IvanLi-CN/ups120/docs/pack_fet_selection.md

## BQ76200 PACK FET 选型报告（DFN5×6）

### 1. 背景与现状

- **电池平台**：项目基于 5S LiFePO₄（≈ 18 V 满电）电池包。SC8815 在异常复位时 VBAT 可能上冲至 ~36 V，需要保证 PACK 级 MOSFET 在该场景下仍安全工作（见 `DESIGN_MEMORANDUM.md`, `SC8815_External_Resistor_Configuration.md`）。
- **PACK 级拓扑**：根据最新网表 `docs/battery-pcb/netlist_battery.enet`，BQ76200（U3）通过 `CHG` / `DSG` 驱动两组背靠背 MOSFET：
  - **Q4 / Q8**：`NCEP6090AGU`（60 V, 90 A, DFN5×6-8L），源极接 `BAT`，漏极与对侧 FET 共结点 `$1N13010`。
  - **Q5 / Q9**：`NCEP40T13GU`（40 V, 130 A, DFN5×6-8L），源极接 `PACK_INNER_+`，漏极同样连接 `$1N13010`。
  - BQ76200 引脚 `CHG_EN/DSG_EN` 通过 nets `$1N12659`、`$1N12649` 分别控制 Q5/Q9 与 Q4/Q8 的栅极。
- **外部防护**：`D1 = SMBJ22A`（Vrwm=22 V, Vclamp≈35.5 V）位于 `PACK_INNER_+` 与 GND 之间，用于吸收负载侧感性尖峰。

> 结论：当前只有靠近电池侧的 FET（Q4/Q8）已换成 60 V 规格，靠近输出侧的 Q5/Q9 仍为 40 V 器件，在 VBAT 异常或 TVS 钳位上沿（≈35.5 V）时耐压裕量不足。

### 2. 驱动与选型约束

- **驱动能力**：BQ76200 内部充泵输出 9–14 V，等效上拉电阻约 1.1 kΩ、下拉 0.3 kΩ（TI SLUSC16B §6.5, §6.6）。对 40–90 nC 量级门电荷，开关时间在 5–10 µs，可满足保护动作需求。
- **耐压要求**：
  - 静态：5S LiFePO₄ 满电 ~18 V。
  - 异常：SC8815 寄存器复位引起 VBAT≈36 V。
  - 负载尖峰：由 D1 将 PACK 端限制在 35.5 V 左右。
  - 因此建议 FET V<sub>DS</sub> ≥ 60 V，优选 ≥ 65 V 以覆盖元件容差与 PCB 走线寄生。
- **封装兼容性**：现有 PCB 使用 DFN5×6-8L（Pad 尺寸 5.8×4.9 mm）。优先选择同封装以避免改版。

### 3. 备选器件比较（DFN5×6-8L）

| 型号 | V<sub>DS</sub> | Qg (typ) | Ciss | R<sub>DS(on)</sub> (典型) | I<sub>D</sub> (25 °C) | 单价 (¥)* | 资料 |
|---|---|---|---|---|---|---|---|
| **NCEP60T15G** | 60 V | 47 nC @10 V | 2.65 nF | 3.0 mΩ @10 V / 5.0 mΩ @4.5 V | 100 A | 2.65 | VBsemi `NCEP60T15G-VB.pdf` |
| **NCEP6090AGU** | 60 V | 67 nC @30 V | 4.00 nF | 2.8 mΩ @10 V / 3.5 mΩ @4.5 V | 90 A | 1.96 | NCE `ncep6090agu.pdf` |
| **NCEP035N85GU** | 85 V | 88 nC @10 V | 4.95 nF | 2.9 mΩ @10 V | 135 A | 2.94 | NCE `NCEP035N85GU.pdf` |

> *单价为同一渠道 2025-10-29 批量零购参考价（不含邮费），用于对比相对成本，实际采购以当期报价为准。

> 以上器件均与现有焊盘兼容，且门电荷在 BQ76200 的驱动能力范围之内。

### 4. 适配性评估

1. **耐压余量**  
   - 60 V 器件对 36 V 异常 + TVS 35.5 V 仍保留 >60 % 额定余量；40 V 器件裕量不足。  
   - 若外部系统可能施加更高母线或浪涌，可考虑 80–100 V 器件（如 NCEP035N85GU），但需评估额外门电荷与损耗。

2. **导通损耗与热**  
   - NCEP60T15G 和 TPHR6504PL 在 4.5–6 V 驱动下 R<sub>DS(on)</sub> 较低，有利于减小发热。  
   - NCEP6090AGU 已在 Q4/Q8 使用，可直接平移到 Q5/Q9，便于库存及 BOM 管理。  

3. **驱动裕度**  
   - BQ76200 以 1.1 kΩ 上拉驱动 50–90 nC 门电荷，开通时间约 5–8 µs（Qg ÷ (Vgate / R)）。与 datasheet 针对 10 nF 负载给出的 27–45 µs 设计值相比仍然留有余量。  
   - 更高 Qg（≥120 nC）器件会拖慢保护动作，不推荐。

### 5. 推荐方案

1. **统一更换 Q5 / Q9 为 60 V 器件**（保持 Q4 / Q8 为 60 V；形成四颗相同型号）  
   - **优选型号**：`NCEP60T15G`（低 Qg、低 R<sub>DS(on)</sub>），或直接延用 `NCEP6090AGU` 以简化供应。  
   - 若考虑 EMC/热设计极限，可评估 `TPHR6504PL` 作为备选。  
   - 高耐压备选 `NCEP035N85GU` 仅在需要额外裕度时使用，需要验证 6 V 驱动下的损耗。

2. **保留 SC8815 同步 FET（Q2/Q3/Q6/Q7）**：这几颗仍是 NCEP4090GU（40 V），仅承受电感两端电压，不直接面对 PACK 侧浪涌，本次无需调整。

### 6. 实施与验证计划

1. **BOM / 原理图更新**：将 Q5/Q9 型号改为推荐器件，并在 `docs/battery-pcb/netlist_battery.enet` 中保持一致。  
2. **样机验证**：焊接新 MOS 后，进行以下测试：  
   - 充电通路异常复位（VBAT≈36 V），确认 V<sub>DS</sub> 与温升。  
   - 放电通路断开感性负载，示波 PACK 电压，确认 TVS 钳位与 MOSFET 未过压。  
   - 长时间放电 / 充电，采集 FET 结温与效率。
3. **驱动波形检查**：测量 BQ76200 `CHG/DSG` 输出栅波形，必要时在栅极串入 1–2 Ω 阻尼以抑制振铃。  
4. **文件同步**：测试完成后，将结论写入 `DESIGN_MEMORANDUM.md`，并更新量产 BOM。

### 7. 结语

通过将 PACK 侧所有 DFN5×6 MOSFET 统一提升至 60 V 等级，可显著提高面对 VBAT 异常与外部尖峰的耐压裕度，同时保持与原 PCB 焊盘、电气驱动兼容。请在下一轮样机验证中重点关注动态浪涌与热表现，确认满足整机寿命与安全要求。***
