IvanLi-CN/ups120/docs/STM32L051C8_Index.md

# STM32L051C8 Datasheet (Markdown Parts)

Source: stm32l051c8.pdf

Parts:
- [Part 1: Pages 1–50](stm32l051c8/STM32L051C8_Part_001.md)
- [Part 2: Pages 51–100](stm32l051c8/STM32L051C8_Part_002.md)
- [Part 3: Pages 101–133](stm32l051c8/STM32L051C8_Part_003.md)
