IvanLi-CN/ups120/docs/rm0377/RM0377_STM32L0x1_Part_004.md

# RM0377 STM32L0x1 — Pages 151–200

**RM0377** **Power control (PWR)**

**6.3.7** **Sleep mode**

**I/O states in Sleep mode**

In Sleep mode, all I/O pins keep the same state as in Run mode.

**Entering Sleep mode**

The Sleep mode is entered according to _Section 6.3.5: Entering low-power mode_ .

Refer to _Table 35: Sleep-now_ and _Table 36: Sleep-on-exit_ for details on how to enter Sleep
mode.

**Exiting Sleep mode**

The Sleep mode is exited according to _Section 6.3.6: Exiting low-power mode_ .

Refer to _Table 35: Sleep-now_ and _Table 36: Sleep-on-exit_ for more details on how to exit
Sleep mode.

**Table 35. Sleep-now**

|Sleep-now mode|Description|
|---|---|
|Mode entry|WFI (Wait for Interrupt) or WFE (Wait for Event) while:<br>– SLEEPDEEP = 0 and<br>– No interrupt (for WFI) or event (for WFE) is pending<br>Refer to the Cortex®-M0+ System Control register (see PM0223 programming<br>manual).|
|Mode entry|On return from ISR while:<br>– SLEEPDEEP = 0 and<br>– SLEEPONEXIT = 1 and<br>– No interrupt is pending<br>Refer to the Cortex®-M0+ System Control register (see PM0223 programming<br>manual).|
|Mode exit|If WFI or return from ISR was used for entry:<br>Interrupt: refer to_Table 53: List of vectors_<br>If WFE was used for entry and SVONPEND = 0<br>Wakeup event: refer to_Section 12.3.2: Wakeup event management_<br>If WFE was used for entry and SVONPEND = 1<br>Interrupt event when disabled in NVIC (refer to_Table 53: List of vectors)_or<br>wakeup event (refer to_Section 12.3.2: Wakeup event management_)|
|Wakeup latency|None|

RM0377 Rev 10 151/905

166

--- end of page=150 ---

**Power control (PWR)** **RM0377**

**Table 36. Sleep-on-exit**

|Sleep-on-exit|Description|
|---|---|
|Mode entry|WFI (wait for interrupt) while:<br>– SLEEPDEEP = 0 and<br>– No interrupt (for WFI) or event (for WFE) is pending<br>Refer to the Cortex®-M0+ System Control register (see PM0223<br>programming manual).|
|Mode entry|On return from ISR while:<br>– SLEEPDEEP = 0 and<br>– SLEEPONEXIT = 1 and<br>– No interrupt is pending<br>Refer to the Cortex®-M0+ System Control register (see PM0223<br>programming manual).|
|Mode exit|Interrupt: refer to_Table 53: List of vectors_|
|Wakeup latency|None|

**6.3.8** **Low-power sleep mode (LP sleep)**

**I/O states in Low-power sleep mode**

In Low-power sleep mode, all I/O pins keep the same state as in Run mode.

**Entering Low-power sleep mode**

To enter Low-power sleep mode, proceed as follows:

1. The Flash memory can be switched off by using the control bits (SLEEP_PD in the
FLASH_ACR register. This reduces power consumption but increases the wake-up
time.

2. Each digital IP clock must be enabled or disabled by using the RCC_APBxENR and
RCC_AHBENR registers.

3. The frequency of the system clock must be decreased.

4. The regulator is forced in low-power mode by software (LPSDSR bits set).

5. Follow the steps described in _Section 6.3.5: Entering low-power mode_ .

Refer to _Table 37: Sleep-now (Low-power sleep)_ and _Table 38: Sleep-on-exit (Low-power_
_sleep)_ for details on how to enter Low-power sleep mode.

In Low-power sleep mode, the Flash memory can be switched off and the RAM memory
remains available.

In this mode, the system frequency should not exceed f_MSI range1.

Please refer to product datasheet for more details on voltage regulator and peripherals
operating conditions.

Low-power sleep mode can only be entered when V CORE is in range 2.

152/905 RM0377 Rev 10

--- end of page=151 ---

**RM0377** **Power control (PWR)**

_Note:_ _To be able to read the RTC calendar register when the APB1 clock frequency is less than_
_seven times the RTC clock frequency (7*RTCLCK), the software must read the calendar_
_time and date registers twice._

_If the second read of the RTC_TR gives the same result as the first read, this ensures that_
_the data is correct. Otherwise a third read access must be done._

**Exiting Low-power sleep mode**

The Low-power sleep mode is exited according to _Section 6.3.6: Exiting low-power mode_ .

When exiting Low-power sleep mode by issuing an interrupt or a wakeup event, the
regulator is configured in Main regulator mode, the Flash memory is switched on (if
necessary), and the system clock can be increased.

When the voltage regulator operates in low-power mode, an additional startup delay is
incurred when waking up from Low-power sleep mode.

Refer to _Table 37: Sleep-now (Low-power sleep)_ and _Table 38: Sleep-on-exit (Low-power_
_sleep)_ for more details on how to exit Sleep low-power mode.

**Table 37. Sleep-now (Low-power sleep)**

|Sleep-now mode|Description|
|---|---|
|Mode entry|Voltage regulator in low-power mode and the Flash memory switched off<br>WFI (Wait for Interrupt) or WFE (wait for event) while:<br>– SLEEPDEEP = 0 and<br>– No interrupt (for WFI) or event (for WFE) is pending<br>Refer to the Cortex®-M0+ System Control register (see PM0223 programming<br>manual).|
|Mode entry|On return from ISR while:<br>– SLEEPDEEP = 0 and<br>– SLEEPONEXIT = 1 and<br>– No interrupt is pending<br>Refer to the Cortex®-M0+ System Control register (see PM0223 programming<br>manual).|
|Mode exit|Voltage regulator in Main regulator mode and the Flash memory switched on<br>If WFI or Return from ISR was used for entry:<br>Interrupt: Refer to_Table 53: List of vectors_<br>If WFE was used for entry and SEVONPEND = 0<br>Wakeup event: Refer to_Section 12.3.2: Wakeup event management_<br>If WFE was used for entry and SVONPEND = 1<br>Interrupt event when disabled in NVIC (refer to_Table 53: List of vectors)_or<br>wakeup event (refer to_Section 12.3.2: Wakeup event management_)|
|Wakeup latency|Regulator wakeup time from low-power mode|

RM0377 Rev 10 153/905

166

--- end of page=152 ---

**Power control (PWR)** **RM0377**

**Table 38. Sleep-on-exit (Low-power sleep)**

|Sleep-on-exit|Description|
|---|---|
|Mode entry|WFI (wait for interrupt) while:<br>– SLEEPDEEP = 0 and<br>– No interrupt (for WFI) or event (for WFE) is pending<br>Refer to the Cortex®-M0+ System Control register (see PM0223<br>programming manual).|
|Mode entry|On return from ISR while:<br>– SLEEPDEEP = 0 and<br>– SLEEPONEXIT = 1 and<br>– No interrupt is pending<br>Refer to the Cortex®-M0+ System Control register (see PM0223<br>programming manual).|
|Mode exit|Interrupt: refer to_Table 53: List of vectors_.|
|Wakeup latency|regulator wakeup time from low-power mode|

**6.3.9** **Stop mode**

The Stop mode is based on the Cortex [®] -M0+ Deepsleep mode combined with peripheral
clock gating. The voltage regulator can be configured either in normal or low-power mode.
In Stop mode, all clocks in the V CORE domain are stopped, the PLL, the MSI, the HSI16
(except if HSI16KERON is set in Stop mode, see _Section 7.3.1: Clock control register_
_(RCC_CR)_ ) and the HSE RC oscillators are disabled. Internal SRAM and register contents
are preserved.

To get the lowest consumption in Stop mode, the internal Flash memory also enters lowpower mode. When the Flash memory is in power-down mode, an additional startup delay is
incurred when waking up from Stop mode.

To minimize the consumption In Stop mode, V REFINT, the BOR, PVD, and temperature
sensor can be switched off before entering Stop mode. This functionality is controlled by the
ULP bit in the PWR_CR register. If the ULP bit is set, the reference is switched off on Stop
mode entry and enabled again on wakeup. .

**I/O states in Low-power sleep mode**

In Stop mode, all I/O pins keep the same state as in Run mode.

**Entering Stop mode**

Refer to _Section 6.3.5: Entering low-power mode_ and to _Table 39_ for details on how to enter
the Stop mode.

If the application needs to disable the external clock before entering Stop mode, the HSEON
bit must be first disabled and the system clock switched to HSI16.

Otherwise, if the HSEON bit is kept enabled while external clock (external oscillator) can be
removed before entering Stop mode, the clock security system (CSS) feature must be
enabled to detect any external oscillator failure and avoid a malfunction behavior when
entering Stop mode.

154/905 RM0377 Rev 10

--- end of page=153 ---

**RM0377** **Power control (PWR)**

To further reduce power consumption in Stop mode, the internal voltage regulator can be put
in low-power mode. This is configured by the LPSDSR or LPDS bit in the PWR_CR register
(see _Section 6.4.1_ ). The internal voltage regulator can also be kept in Main mode but the
consumption will be much higher. As a result, it is always implicitly assumed that the
regulator is in low-power mode during Stop mode. The only advantage of keeping the
regulator in Main mode is that the wakeup time from Stop mode is shorter.

If Flash memory programming or an access to the APB domain is ongoing, the Stop mode
entry is delayed until the memory or APB access has completed.

In Stop mode, the following features can be selected by programming individual control bits:

      - Independent watchdog (IWDG): the IWDG is started by writing to its Key register or by
hardware option. Once started it cannot be stopped except by a Reset. Refer to
_Section 20.3: IWDG functional description_ in _Section 20: Independent watchdog_
_(IWDG)_ .

      - Real-time clock (RTC): this is configured by the RTCEN bit in the RCC_CSR register
(see _Section 7.3.20_ ).

      - Internal RC oscillator (LSI RC): this is configured by the LSION bit in the RCC_CSR
register.

      - External 32.768 kHz oscillator (LSE OSC): this is configured by the LSEON bit in the
RCC_CSR register.

The ADC can also consume power in Stop mode, unless they are disabled before entering
it. To disable them, the ADDIS bit in the ADC_CR register must be set to 1 must be written
to 0.

**Exiting Stop mode**

Refer to _Section 6.3.6: Exiting low-power mode_ and to _Table 39_ for details on how to exit
Stop mode.

When exiting Stop mode by issuing an interrupt or a wakeup event, the MSI or HSI16 RC
oscillator is selected as system clock depending the bit STOPWUCK in the RCC_CFGR
register.

When the voltage regulator operates in low-power mode, an additional startup delay is
incurred when waking up from Stop mode. By keeping the internal regulator ON during Stop
mode, the consumption is higher although the startup time is reduced.

RM0377 Rev 10 155/905

166

--- end of page=154 ---

**Power control (PWR)** **RM0377**

**Table 39. Stop mode**

|Stop mode|Description|
|---|---|
|Mode entry|WFI (Wait for Interrupt) or WFE (Wait for Event) while:<br>– No interrupt (for WFI) or event (for WFE) is pending.<br>– SLEEPDEEP bit is set in Cortex®-M0+ System Control register<br>– PDDS bit = 0 in Power Control register (PWR_CR)<br>– WUF bit = 0 in Power Control/Status register (PWR_CSR)<br>– MSI or HSI16 RC oscillator are selected as system clock for Stop mode<br>exit by configuring the STOPWUCK bit in the RCC_CFGR register.<br>_Note: To enter the Stop mode, all EXTI Line pending bits (in_<br>_Section 12.5.6: EXTI pending register (EXTI_PR)), all peripherals_<br>_interrupt pending bits, the RTC Alarm (Alarm A and Alarm B), RTC_<br>_wakeup, RTC tamper, and RTC time-stamp flags, must be reset._<br>_Otherwise, the Stop mode entry procedure is ignored and program_<br>_execution continues._|
|Mode entry|On return from ISR while:<br>– No interrupt is pending.<br>– SLEEPDEEP bit is set in Cortex®-M0+ System Control register<br>– SLEEPONEXIT = 1<br>– PDDS bit = 0 in Power Control register (PWR_CR)<br>– WUF bit = 0 in Power Control/Status register (PWR_CSR)<br>– MSI or HSI16 RC oscillator are selected as system clock for Stop mode<br>exit by configuring the STOPWUCK bit in the RCC_CFGR register.<br>_Note: To enter the Stop mode, all EXTI Line pending bits (in_<br>_Section 12.5.6: EXTI pending register (EXTI_PR)), all peripherals_<br>_interrupt pending bits, the RTC Alarm (Alarm A and Alarm B), RTC_<br>_wakeup, RTC tamper, and RTC time-stamp flags, must be reset._<br>_Otherwise, the Stop mode entry procedure is ignored and program_<br>_execution continues._|
|Mode exit|If WFI or return from ISR was used for entry:<br>Any EXTI Line configured in Interrupt mode (the corresponding EXTI<br>Interrupt vector must be enabled in the NVIC). Refer to_Table 53: List of_<br>_vectors._<br>If WFE was used for entry and SEVONPEND = 0<br>Any EXTI Line configured in event mode. Refer to_Section 12.3.2:_<br>_Wakeup event management on page 269_<br>If WFE was used for entry and SEVONPEND = 1<br>– Any EXTI Line configured in event mode (even if the corresponding EXTI<br>interrupt is disabled in the NVIC). The interrupt source can be an external<br>interrupt or a peripheral with wakeup capability (refer to_Table 53: List of_<br>_vectors)._<br>– A wakeup event (refer to_Section 12.3.2: Wakeup event management on_<br>_page 269_)|
|Wakeup latency|MSI or HSI16 RC wakeup time + regulator wakeup time from Low-power<br>mode + FLASH wakeup time|

156/905 RM0377 Rev 10

--- end of page=155 ---

**RM0377** **Power control (PWR)**

**6.3.10** **Standby mode**

The Standby mode allows to achieve the lowest power consumption. It is based on the
Cortex [®] -M0+ Deepsleep mode, with the voltage regulator disabled. The V CORE domain is
consequently powered off. The PLL, the MSI, the HSI16 oscillator and the HSE oscillator
are also switched off. SRAM and register contents are lost except for the RTC registers,
RTC backup registers and Standby circuitry (see _Figure 10_ ).

**I/O states in Standby mode**

In Standby mode, all I/O pins are high impedance except for:

      - Reset pad

      - Wakeup pins (WKUP1, WKUP2, WKUP3)

      - RTC functions (tamper, time-stamp, RTC Alarm out, RTC clock calibration out) on the
following I/Os:

–
Category 1: PA0, PA2

–
Category 2: PC13, PA0, PA2

–
Category 3: PC13, PA0

–
Category 5: PC13, PA0, PE6

**Entering Standby mode**

Refer to _Section 6.3.5: Entering low-power mode_ and to _Table 40_ for details on how to enter
Standby mode.

In Standby mode, the following features can be selected by programming individual control
bits:

      - Independent watchdog (IWDG): the IWDG is started by writing to its Key register or by
hardware option. Once started it cannot be stopped except by a reset. Refer to
_Section 20.3: IWDG functional description on page 528_ .

      - Real-time clock (RTC): this is configured by the RTCEN bit in the RCC_CSR register
(see _Section 7.3.20_ ).

      - Internal RC oscillator (LSI RC): this is configured by the LSION bit in the RCC_CSR
register.

      - External 32.768 kHz oscillator (LSE OSC): this is configured by the LSEON bit in the
RCC_CSR register.

**Exiting Standby mode**

The microcontroller exits Standby mode when an external Reset (NRST pin), an IWDG
Reset, a rising edge on WKUP pins (WUKP1, WKUP2 or WKUP3), an RTC alarm, a tamper
event, or a time-stamp event is detected.

After waking up from Standby mode, program execution restarts in the same way as after a
Reset (boot pins sampling, vector reset is fetched, etc.). The SBF status flag in the
PWR_CSR register (see _Section 6.4.2_ ) indicates that the microcontroller was in Standby
mode. All registers are reset to their default value after a system reset except for the register
bits in the RTC domain (see _Section 22.7: RTC registers_, SBF status flag in the _PWR power_
_control/status register (PWR_CSR)_, _Control/status register (RCC_CSR)_ and _Clock control_
_register (RCC_CR)_ ).

Refer to _Section 6.3.6: Exiting low-power mode_ and to _Table 40_ for more details on how to
exit Standby mode.

RM0377 Rev 10 157/905

166

--- end of page=156 ---

**Power control (PWR)** **RM0377**

**Table 40. Standby mode**

|Standby mode|Description|
|---|---|
|Mode entry|WFI (Wait for Interrupt) or WFE (Wait for Event) while:<br>– SLEEPDEEP = 1 in Cortex®-M0+ System Control register<br>– PDDS = 1 bit in Power Control register (PWR_CR)<br>– No interrupt (for WFI) or event (for WFE) is pending.<br>– WUF = 0 bit in Power Control/Status register (PWR_CSR)<br>– the RTC flag corresponding to the chosen wakeup source (RTC Alarm A,<br>RTC Alarm B, RTC wakeup, Tamper or Time-stamp flags) is cleared|
|Mode entry|On return from ISR while:<br>– SLEEPDEEP = 1 in Cortex®-M0+ System Control register<br>– SLEEPONEXIT = 1<br>– PDDS bit = 1 in Power Control register (PWR_CR)<br>– No interrupt is pending.<br>– WUF bit = 0 in Power Control/Status register (PWR_CSR)<br>– the RTC flag corresponding to the chosen wakeup source (RTC Alarm A,<br>RTC Alarm B, RTC wakeup, Tamper or Time-stamp flags) is cleared.|
|Mode exit|WKUP pin rising edge, RTC alarm (Alarm A and Alarm B), RTC wakeup,<br>tamper event, time-stamp event, external reset in NRST pin, IWDG reset.|
|Wakeup latency|Reset phase|

**Debug mode**

By default, the debug connection is lost if the application puts the MCU in Stop or Standby
mode while the debug features are used. This is due to the fact that the Cortex [®] -M0+ core is
no longer clocked.

However, by setting some configuration bits in the DBG_CR register, the software can be
debugged even when using the low-power modes extensively. For more details, refer to
_Section 27.9.1: Debug support for low-power modes_ .

**6.3.11** **Waking up the device from Stop and Standby modes using the RTC**
**and comparators**

The MCU can be woken up from low-power mode by an RTC Alarm event, an RTC Wakeup
event, a tamper event, a time-stamp event, or a comparator event, without depending on an
external interrupt (Auto-wakeup mode).

These RTC alternate functions can wake up the system from Stop and Standby low-power
modes while the comparator events can only wake up the system from Stop mode.

The system can also wake up from low-power modes without depending on an external
interrupt (Auto-wakeup mode) by using the RTC alarm or the RTC wakeup events.

158/905 RM0377 Rev 10

--- end of page=157 ---

**RM0377** **Power control (PWR)**

The RTC provides a programmable time base for waking up from Stop or Standby mode at
regular intervals. For this purpose, two of the three alternative RTC clock sources can be
selected by programming the RTCSEL[1:0] bits in the RCC_CSR register (see
_Section 7.3.20_ ):

      - Low-power 32.768 kHz external crystal oscillator (LSE OSC).
This clock source provides a precise time base with very low-power consumption (less
than 1 µA added consumption in typical conditions)

      - Low-power internal RC oscillator (LSI RC)

This clock source has the advantage of saving the cost of the 32.768 kHz crystal. This
internal RC Oscillator is designed to use minimum power consumption.

**RTC auto-wakeup (AWU) from the Stop mode**

      - To wake up from the Stop mode with an RTC alarm event, it is necessary to:

a) Configure the EXTI Line 17 to be sensitive to rising edges (Interrupt or Event
modes)

b) Enable the RTC Alarm interrupt in the RTC_CR register

c) Configure the RTC to generate the RTC alarm

      - To wake up from the Stop mode with an RTC Tamper or time stamp event, it is
necessary to:

a) Configure the EXTI Line 19 to be sensitive to rising edges (Interrupt or Event
modes)

b) Enable the RTC TimeStamp Interrupt in the RTC_CR register or the RTC Tamper
Interrupt in the RTC_TCR register

c) Configure the RTC to detect the tamper or time stamp event

      - To wake up from the Stop mode with an RTC Wakeup event, it is necessary to:

a) Configure the EXTI Line 20 to be sensitive to rising edges (Interrupt or Event
modes)

b) Enable the RTC Wakeup Interrupt in the RTC_CR register

c) Configure the RTC to generate the RTC Wakeup event

**RTC auto-wakeup (AWU) from the Standby mode**

      - To wake up from the Standby mode with an RTC alarm event, it is necessary to:

a) Enable the RTC Alarm interrupt in the RTC_CR register

b) Configure the RTC to generate the RTC alarm

      - To wake up from the Stop mode with an RTC Tamper or time stamp event, it is
necessary to:

a) Enable the RTC TimeStamp Interrupt in the RTC_CR register or the RTC Tamper
Interrupt in the RTC_TCR register

b) Configure the RTC to detect the tamper or time stamp event

      - To wake up from the Stop mode with an RTC Wakeup event, it is necessary to:

a) Enable the RTC Wakeup Interrupt in the RTC_CR register

b) Configure the RTC to generate the RTC Wakeup event

RM0377 Rev 10 159/905

166

--- end of page=158 ---

**Power control (PWR)** **RM0377**

**Comparator auto-wakeup (AWU) from the Stop mode**

      - To wake up from the Stop mode with a comparator 1 or comparator 2 wakeup event, it
is necessary to:

a) Configure the EXTI Line 21 for comparator 1 or EXTI Line 22 for comparator 2
(Interrupt or Event mode) to be sensitive to the selected edges (falling, rising or
falling and rising)

b) Configure the comparator to generate the event.

160/905 RM0377 Rev 10

--- end of page=159 ---

**RM0377** **Power control (PWR)**

###### **6.4 Power control registers**

The peripheral registers have to be accessed by half-words (16-bit) or words (32-bit).

**6.4.1** **PWR power control register (PWR_CR)**

Address offset: 0x00

Reset value: 0x0000 1000 (reset by wakeup from Standby mode)

|31|30|29|28|27|26|25|24|23|22|21|20|19|18|17|16|
|---|---|---|---|---|---|---|---|---|---|---|---|---|---|---|---|
|Res.|Res.|Res.|Res.|Res.|Res.|Res.|Res.|Res.|Res.|Res.|Res.|Res.|Res.|Res.|LPDS|
||||||||||||||||rw|

|15|14|13|12 11|Col5|10|9|8|7 6 5|Col10|Col11|4|3|2|1|0|
|---|---|---|---|---|---|---|---|---|---|---|---|---|---|---|---|
|Res.|LPRUN|DS_EE<br>_KOFF|VOS[1:0]|VOS[1:0]|FWU|ULP|DBP|PLS[2:0]|PLS[2:0]|PLS[2:0]|PVDE|CSBF|CWUF|PDDS|LPSDSR|
||rw|rw|rw|rw|rw|rw|rw|rw|rw|rw|rw|rc_w1|rc_w1|rw|rw|

Bits 31:17 Reserved, always read as 0.

Bit 16 **LPDS** : Regulator in Low-power deepsleep mode

This bit allows switching the regulator to low-power mode when the CPU enters Stop
mode. Its behavior depends on LPSDSR bit.

– if LPSDSR = 1: bit has no effect.

– if LPSDSR = 0:

0: Voltage regulator in Main mode during Deepsleep mode (Stop mode)
1: Voltage regulator switches to low-power mode when the CPU enters Deepsleep mode
(Stop mode).
The regulator goes back to Main mode when the CPU exits from Deepsleep mode.

_Note: The LPDS bit is available on category 1 devices only._

Bit 15 Reserved, always read as 0.

Bit 14 **LPRUN:** Low-power run mode

When LPRUN bit is set together with the LPSDSR bit, the regulator is switched from Main
mode to low-power mode. Otherwise, it remains in Main mode. The regulator goes back to
operate in Main mode when LPRUN is reset.
If this bit is set (with LPSDSR bit set) and the CPU enters sleep or Deepsleep mode (LP
sleep or Stop mode), then, when the CPU wakes up from these modes, it enters Run
mode but with LPRUN bit set. To enter again Low-power run mode, it is necessary to
perform a reset and set LPRUN bit again.
It is forbidden to reset LPSDSR when the MCU is in Low-power run mode. LPSDSR is
used as a prepositioning for the entry into low-power mode, indicating to the system which
configuration of the regulator will be selected when entering low-power mode. The
LPSDSR bit must be set before the LPRUN bit is set. LPSDSR can be reset only when
LPRUN bit=0.

0: Voltage regulator in Main mode in Low-power run mode
1: Voltage regulator in low-power mode in Low-power run mode

Bit 13 **DS_EE_KOFF** : Deepsleep mode with non-volatile memory kept off

When entering low-power mode (Stop or Standby only), if DS_EE_KOFF and RUN_PD
bits are both set in FLASH_ACR register (refer to _Section 3.7.1: Access control register_
_(FLASH_ACR)_, the non-volatile memory (Flash program memory and data EEPROM) will
not be woken up when exiting from Deepsleep mode.
0: NVM woken up when exiting from Deepsleep mode even if the bit RUN_PD is set
1: NVM not woken up when exiting from low-power mode (if the bit RUN_PD is set)

RM0377 Rev 10 161/905

166

--- end of page=160 ---

**Power control (PWR)** **RM0377**

Bits 12:11 **VOS[1:0]:** Voltage scaling range selection

These bits are used to select the internal regulator voltage range.
Before resetting the power interface by resetting the PWRRST bit in the RCC_APB1RSTR
register, these bits have to be set to ‘10’ and the frequency of the system has to be
configured accordingly.

00: forbidden (bits are unchanged and keep the previous value, no voltage change
occurs)
01: 1.8 V (range 1)
10: 1.5 V (range 2)
11: 1.2 V (range 3)

Bit 10 **FWU** : Fast wakeup

This bit works in conjunction with ULP bit.

If ULP = 0, FWU is ignored

If ULP = 1 and FWU = 1: V REFINT startup time is ignored when exiting from low-power mode.
The VREFINTRDYF flag in the PWR_CSR register indicates when the V REFINT is ready
again.

If ULP=1 and FWU = 0: Exiting from low-power mode occurs only when the V REFINT is ready
(after its startup time). This bit is not reset by resetting the PWRRST bit in the
RCC_APB1RSTR register.

0: Low-power modes exit occurs only when V REFINT is ready
1: V REFINT start up time is ignored when exiting low-power modes

Bit 9 **ULP** : Ultra-low-power mode

When set, the V REFINT is switched off in low-power mode. The BOR, PVD, and temperature
sensor also rely on the voltage reference. This bit is not reset by resetting the PWRRST bit
in the RCC_APB1RSTR register.

0: V REFINT is on in low-power mode
1: V REFINT is off in low-power mode

Bit 8 **DBP** : Disable backup write protection

In reset state, the RTC, RTC backup registers and RCC CSR register are protected against
parasitic write access. This bit must be set to enable write access to these registers.

0: Access to RTC, RTC Backup and RCC CSR registers disabled
1: Access to RTC, RTC Backup and RCC CSR registers enabled

_Note: If the HSE divided by 2, 4, 8 or 16 is used as the RTC clock, this bit must remain set_
_to 1._

Bits 7:5 **PLS[2:0]:** PVD level selection

These bits are written by software to select the voltage threshold detected by the
programmable voltage detector:

000: 1.9 V

001: 2.1 V

010: 2.3 V

011: 2.5 V

100: 2.7 V

101: 2.9 V

110: 3.1 V

111: External input analog voltage (Compare internally to V REFINT )
PVD_IN input (PB7) has to be configured as analog input when PLS[2:0] = 111.

_Note: Refer to the electrical characteristics of the datasheet for more details._

162/905 RM0377 Rev 10

--- end of page=161 ---

**RM0377** **Power control (PWR)**

Bit 4 **PVDE:** Programmable voltage detector enable

This bit is set and cleared by software.

0: PVD disabled

1: PVD enabled

Bit 3 **CSBF** : Clear standby flag

This bit is always read as 0.

0: No effect

1: Clear the SBF Standby flag (write).

Bit 2 **CWUF:** Clear wakeup flag

This bit is always read as 0.

0: No effect

1: Clear the WUF Wakeup flag after 2 system clock cycles

Bit 1 **PDDS** : Power-down deepsleep

This bit is set and cleared by software.

0: Enter Stop mode when the CPU enters Deepsleep.
1: Enter Standby mode when the CPU enters Deepsleep.

Bit 0 **LPSDSR:** Low-power deepsleep/Sleep/Low-power run

– DeepSleep/Sleep modes

When this bit is set, the regulator switches in low-power mode when the CPU enters sleep
or Deepsleep mode. The regulator goes back to Main mode when the CPU exits from
these modes.

– Low-power run mode

When this bit is set, the regulator switches in low-power mode when the bit LPRUN is set.
The regulator goes back to Main mode when the bit LPRUN is reset.

This bit is set and cleared by software.

0: Voltage regulator on during Deepsleep/Sleep/Low-power run mode
1: Voltage regulator in low-power mode during Deepsleep/Sleep/Low-power run mode

_Note: If the sequence below is executed:_
_1) Low-power run_
_2) Low-power sleep_
_3) Run_
_4) Low-power run_
_after returning from Low-power deepsleep/Sleep mode (step 2), the regulator goes_
_back to Main mode (step 3). Then to switch to Low-power run mode (step 4), it is_
_necessary to perform a reset and set LPSDSR bit again._

RM0377 Rev 10 163/905

166

--- end of page=162 ---

**Power control (PWR)** **RM0377**

**6.4.2** **PWR power control/status register (PWR_CSR)**

Address offset: 0x04

Reset value: 0x0000 0008 (not reset by wakeup from Standby mode)

Additional APB cycles are needed to read this register versus a standard APB read.

|31|30|29|28|27|26|25|24|23|22|21|20|19|18|17|16|
|---|---|---|---|---|---|---|---|---|---|---|---|---|---|---|---|
|Res.|Res.|Res.|Res.|Res.|Res.|Res.|Res.|Res.|Res.|Res.|Res.|Res.|Res.|Res.|Res.|
|||||||||||||||||

|15|14|13|12|11|10|9|8|7|6|5|4|3|2|1|0|
|---|---|---|---|---|---|---|---|---|---|---|---|---|---|---|---|
|Res.|Res.|Res.|Res.|Res.|EWUP<br>3|EWUP<br>2|EWUP<br>1|Res.|Res.|REG<br>LPF|VOSF|VREFIN<br>TRDYF|PVDO|SBF|WUF|
||||||rw|rw|rw|||r|r|r|r|r|r|

Bits 31:11 Reserved, must be kept at reset value.

Bit 10 **EWUP3** : Enable WKUP pin 3

This bit is set and cleared by software.

0: WKUP pin 3 is used for general purpose I/Os. An event on the WKUP pin 3 does not
wakeup the device from Standby mode.
1: WKUP pin 3 is used for wakeup from Standby mode and forced in input pull down
configuration (rising edge on WKUP pin 3wakes-up the system from Standby mode).

_Note: This bit is reset by a system reset._

Bit 9 **EWUP2** : Enable WKUP pin 2

This bit is set and cleared by software.

0: WKUP pin 2 is used for general purpose I/Os. An event on the WKUP pin 2 does not
wakeup the device from Standby mode.
1: WKUP pin 2 is used for wakeup from Standby mode and forced in input pull down
configuration (rising edge on WKUP pin 2 wakes-up the system from Standby mode).

_Note: This bit is reset by a system reset._

Bit 8 **EWUP1** : Enable WKUP pin 1

This bit is set and cleared by software.

0: WKUP pin 1 is used for general purpose I/Os. An event on the WKUP pin 1 does not
wakeup the device from Standby mode.
1: WKUP pin 1 is used for wakeup from Standby mode and forced in input pull down
configuration (rising edge on WKUP pin 1 wakes-up the system from Standby mode).

_Note: This bit is reset by a system reset._

Bits 7:6 Reserved, must be kept at reset value.

Bit 5 **REGLPF** : Regulator LP flag

This bit is set by hardware when the MCU is in Low-power run mode.

When the MCU exits from Low-power run mode, this bit stays at 1 until the regulator is ready in
Main mode. A polling on this bit is recommended to wait for the regulator Main mode. This bit is
reset by hardware when the regulator is ready.

0: Regulator is ready in Main mode
1: Regulator voltage is in low-power mode

164/905 RM0377 Rev 10

--- end of page=163 ---

**RM0377** **Power control (PWR)**

Bit 4 **VOSF** : Voltage Scaling select flag

A delay is required for the internal regulator to be ready after the voltage range is changed.
The VOSF bit indicates that the regulator has reached the voltage level defined with bits VOS
of PWR_CR register.

This bit is set when VOS[1:0] in PWR_CR register change.
It is reset once the regulator is ready.

0: Regulator is ready in the selected voltage range
1: Regulator voltage output is changing to the required VOS level.

Bit 3 **VREFINTRDYF** : Internal voltage reference (V REFINT ) ready flag
This bit indicates the state of the internal voltage reference, V REFINT .
0: V REFINT is OFF
1: V REFINT is ready

Bit 2 **PVDO:** PVD output

This bit is set and cleared by hardware. It is valid only if PVD is enabled by the PVDE bit.

0: V DD is higher than the PVD threshold selected with the PLS[2:0] bits.
1: V DD is lower than the PVD threshold selected with the PLS[2:0] bits.
_Note: The PVD is stopped by Standby mode. For this reason, this bit is equal to 0 after_
_Standby or reset until the PVDE bit is set._

Bit 1 **SBF:** Standby flag

This bit is set by hardware and cleared only by a POR/PDR (power-on reset/power-down
reset) or by setting the CSBF bit in the _PWR power control register (PWR_CR)_

0: Device has not been in Standby mode
1: Device has been in Standby mode

Bit 0 **WUF:** Wakeup flag

This bit is set by hardware and cleared by a system reset or by setting the CWUF bit in the
_PWR power control register (PWR_CR)_

0: No wakeup event occurred
1: A wakeup event was received from the WKUP pin or from the RTC alarm (Alarm A or
Alarm B), RTC Tamper event, RTC TimeStamp event or RTC Wakeup).

_Note: An additional wakeup event is detected if the WKUP pins are enabled (by setting the_
_EWUPx (x=1, 2, 3) bits) when the WKUP pin levels are already high._

RM0377 Rev 10 165/905

166

--- end of page=164 ---

**Power control (PWR)** **RM0377**

**6.4.3** **PWR register map**

The following table summarizes the PWR registers.

**Table 41. PWR - register map and reset values**

|Offset|Register|31|30|29|28|27|26|25|24|23|22|21|20|19|18|17|16|15|14|13|12|11|10|9|8|7|6|5|4|3|2|1|0|
|---|---|---|---|---|---|---|---|---|---|---|---|---|---|---|---|---|---|---|---|---|---|---|---|---|---|---|---|---|---|---|---|---|---|
|0x000|**PWR_CR**<br><br>|Res.<br>|Res.<br>|Res.<br>|Res.<br>|Res.<br>|Res.<br>|Res.<br>|Res.<br>|Res.<br>|Res.<br>|Res.<br>|Res.<br>|Res.<br>|Res.<br>|Res.<br>|LPDS<br><br>|Res.<br>|LPRUN<br><br>|DS_EE_KOFF.|VOS<br>[1:0]<br><br><br>|VOS<br>[1:0]<br><br><br>|FWU<br><br>|ULP<br><br>|DBP<br>|PLS[2:0]<br><br><br><br>|PLS[2:0]<br><br><br><br>|PLS[2:0]<br><br><br><br>|PVDE<br><br>|CSBF<br><br>|CWUF<br><br>|PDDS<br><br>|LPSDSR<br>|
|0x000|~~Reset value~~||||||||||||||||~~0~~||~~0~~||~~1~~|~~0~~|~~0~~|~~0~~|~~0~~|~~0~~|~~0~~|~~0~~|~~0~~|~~0~~|~~0~~|~~0~~|~~0~~|
|0x004|**PWR_CSR**<br><br>|Res.<br>|Res.<br>|Res.<br>|Res.<br>|Res.<br>|Res.<br>|Res.<br>|Res.<br>|Res.<br>|Res.<br>|Res.<br>|Res.<br>|Res.<br>|Res.<br>|Res.<br>|Res.<br>|Res.<br>|Res.<br>|Res.<br>|Res.<br>|Res.<br>|EWUP3<br><br>|EWUP2<br><br>|EWUP1<br><br>|Res.<br>|Res.<br>|REGLPF<br><br>|VOSF<br><br>|VREFINTRDYF<br><br>|PVDO<br><br>|SBF<br><br>|WUF<br>|
|0x004|~~Reset value~~||||||||||||||||||||||~~0~~|~~0~~|~~0~~|||~~0~~|~~0~~|~~1~~|~~0~~|~~0~~|~~0~~|

Refer to _Section 2.2 on page 51_ for the register boundary addresses.

166/905 RM0377 Rev 10

--- end of page=165 ---

**RM0377** **Reset and clock control (RCC)**

#### **7 Reset and clock control (RCC)**

###### **7.1 Reset**

There are three types of reset, defined as system reset, power reset and RTC domain reset.

**7.1.1** **System reset**

A system reset sets all registers to their reset values unless specified otherwise in the
register description.

A system reset is generated when one of the following events occurs:

      - A low level on the NRST pin (external reset)

      - Window watchdog end-of-count condition (WWDG reset)

      - Independent watchdog end-of-count condition (IWDG reset)

      - A software reset (SW reset) (see _Software reset_ )

      - Low-power management reset (see _Low-power management reset_ )

      - Option byte loader reset (see _Option byte loader reset_ )

      - Exit from Standby mode

      - Firewall protection (see _Section 5: Firewall (FW)_ )

The reset source can be identified by checking the reset flags in the control/status register,
RCC_CSR (see _Section 7.3.20_ ).

**Software reset**

The SYSRESETREQ bit in Cortex [®] -M0+ AIRCR register (Application Interrupt and Reset
Control Register) must be set to force a software reset on the device. Refer to Arm [®]
Cortex [®] -M0+ Technical Reference Manual for more details.

**Low-power management reset**

There are two ways to generate a low-power management reset:

      - Reset generated when entering Standby mode:

This type of reset is enabled by resetting nRST_STDBY bit in user option bytes. In this
case, whenever a Standby mode entry sequence is successfully executed, the device
is reset instead of entering Standby mode.

      - Reset when entering Stop mode:

This type of reset is enabled by resetting nRST_STOP bit in user option bytes. In this
case, whenever a Stop mode entry sequence is successfully executed, the device is
reset instead of entering Stop mode.

**Option byte loader reset**

The Option byte loader reset is generated when the OBL_LAUNCH bit (bit 18) is set in the
FLASH_PECR register. This bit is used to launch by software the option byte loading.

For further information on the user option bytes, refer to _Section 3: Flash program memory_
_and data EEPROM (FLASH)_ .

RM0377 Rev 10 167/905

215

--- end of page=166 ---

**Reset and clock control (RCC)** **RM0377**

**7.1.2** **Power reset**

A power reset is generated when one of the following events occurs:

      - Power-on/power-down reset (POR/PDR reset)

      - BOR reset

A power reset sets all registers to their reset values including for the RTC domain (see
_Figure 16_ )

These sources act on the NRST pin and it is always kept low during the delay phase. The
RESET service routine vector is fixed at address 0x0000_0004 in the memory map. For
more details, refer to _Table 53: List of vectors_ .

The system reset signal provided to the device is output on the NRST pin (except the Exit
from Standby reset which is not output on the NRST pin but generates system reset).

The pulse generator guarantees a minimum reset pulse duration of 20 µs for each internal
reset source. In case of an external reset, the reset pulse is generated while the NRST pin is
asserted low.

When an internal reset occurs, the internal pull-up resistor (RPU) is deactivated in order to
save the power consumption through the pull-up resistor.

**Figure 16. Simplified diagram of the reset circuit**

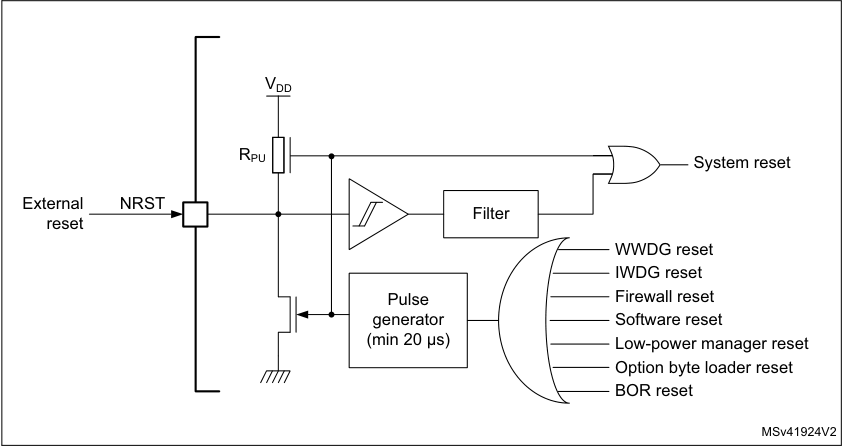
[picture p78: docs/assets/rm0377/rm0377-ultralowpower-stm32l0x1-advanced-armbased-32bit-mcus-stmicroelectronics.pdf-167-0.png]


**7.1.3** **RTC and backup registers reset**

The RTC peripheral, RTC clock source selection (in RCC_CSR) and the backup registers
are reset only when one of the following events occurs:

      - A software reset, triggered by setting the RTCRST bit in the RCC_CSR register (see
_Section 7.3.20_ )

      - Power reset (BOR/POR/PDR).

168/905 RM0377 Rev 10

--- end of page=167 ---

**RM0377** **Reset and clock control (RCC)**

###### **7.2 Clocks**

Four different clock sources can be used to drive the system clock (SYSCLK):

      - HSI16 (high-speed internal) oscillator clock

      - HSE (high-speed external) oscillator clock

The HSE external quartz connexion is available only on cat. 2 devices in LQFP48
package.

      - PLL clock

      - MSI (multispeed internal) oscillator clock

The MSI at 2.1MHz is used as system clock source after startup from power reset,
system or RTC domain reset, and after wake-up from Standby mode.

The HSI16, HSI16 divided by 4, or the MSI at any of its possible frequency can be used
to wake up from Stop mode.

The devices have two secondary clock sources:

      - 37 kHz low speed internal RC (LSI RC) which drives the independent watchdog and
optionally the RTC used for Auto-wakeup from Stop/Standby mode and the LPTIMER.

      - 32.768 kHz low speed external crystal (LSE crystal) which optionally drives the realtime clock (RTCCLK), the LPTIMER and USARTs.

Each clock source can be switched on or off independently when it is not used to optimize
power consumption.

Several prescalers can be used to configure the AHB frequency and the two APBs (APB1
and APB2) domains. The maximum frequency of AHB, APB1 and the APB2 domains is
32 MHz. It depends on the device voltage range. For more details refer to _Section 6.1.4:_
_Dynamic voltage scaling management_ .

All the peripheral clocks are derived from the system clock (SYSCLK) except:

      - The ADC can be derived either from the APB clock or the HSI16 clock.

      - The LPUART1 and USART1/2 clock which is derived (selected by software) from one
of the four following sources:

–
system clock

– HSI16 clock

– LSE clock

–
APB clock (PCLK)

      - The I2C1 clock which is derived (selected by software) from one of the three following

sources:

–
system clock

– HSI16 clock

–
APB clock (PCLK)

      - The LPTIMER clock which is derived (selected by software) from one of the four
following sources:

– HSI16 clock

– LSE clock

– LSI clock

–
APB clock (PCLK)

RM0377 Rev 10 169/905

215

--- end of page=168 ---

**Reset and clock control (RCC)** **RM0377**

      - The RTC clock which is derived from the following clock sources:

–
LSE clock,

–
LSI clock,

–
4 MHz HSE_RTC (HSE divided by a programmable prescaler).

      - IWDG clock which is always the LSI clock.

The system clock (SYSCLK) frequency must be higher or equal to the RTC clock frequency.

The RCC feeds the Cortex [®] System Timer (SysTick) external clock with the AHB clock
(HCLK) divided by 8. The SysTick can work either with this clock or with the Cortex [®] clock
(HCLK), configurable in the SysTick Control and Status Register.

170/905 RM0377 Rev 10

--- end of page=169 ---

**RM0377** **Reset and clock control (RCC)**

**Figure 17. Clock tree**

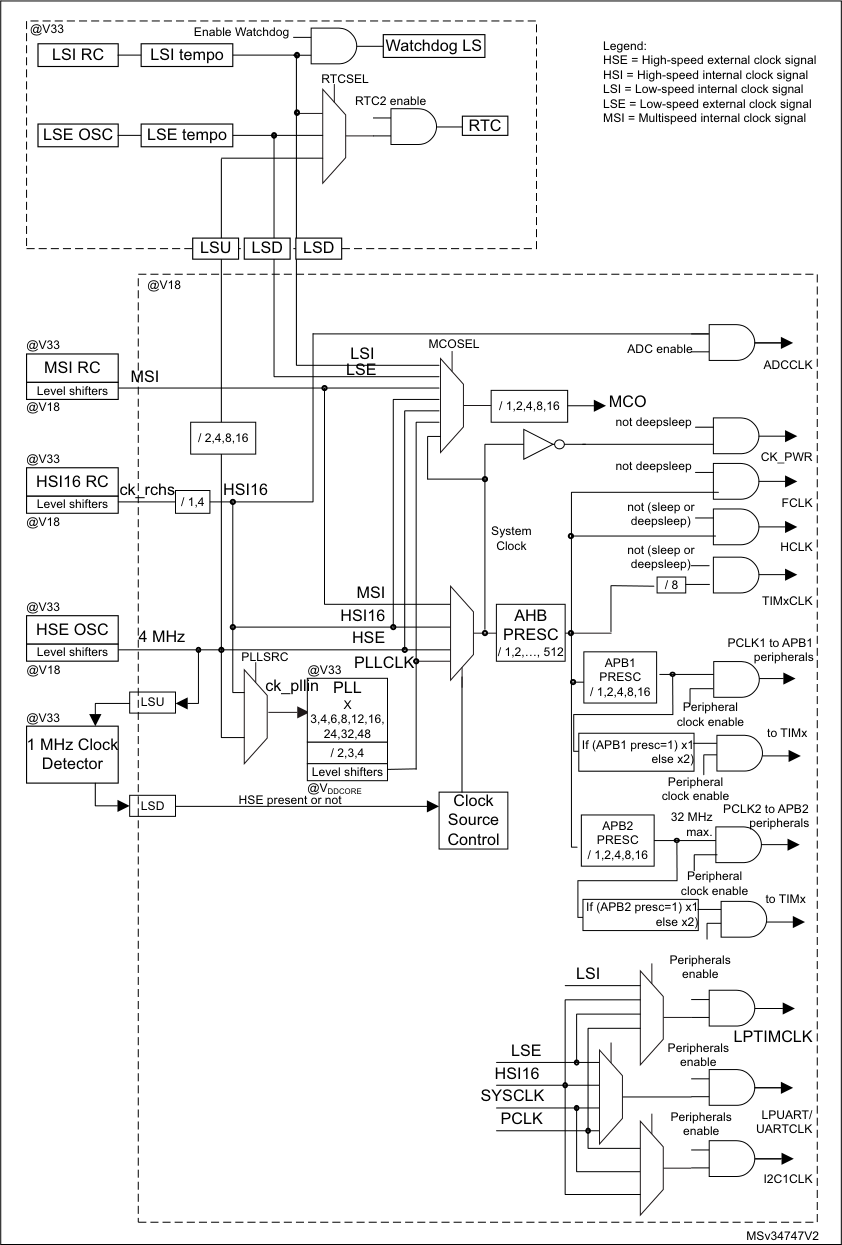
[picture p79: docs/assets/rm0377/rm0377-ultralowpower-stm32l0x1-advanced-armbased-32bit-mcus-stmicroelectronics.pdf-170-0.png]


|Col1|Col2|Col3|Col4|Col5|Col6|Col7|Col8|Col9|Col10|
|---|---|---|---|---|---|---|---|---|---|
|||||||||||
|||||||||||
|||||||||||
||LS||LS||LSD|LSD|LSD|LSD|LSD|
||LS|||||||||
|@V18<br>SI|@V18<br>SI|@V18<br>SI|@V18<br>SI|@V18<br>SI|@V18<br>SI|@V18<br>SI|@V18<br>SI|@V18<br>SI|@V18<br>SI|
|@V18<br>SI|@V18<br>SI|@V18<br>SI|@V18<br>SI|@V18<br>SI|@V18<br>SI|LSE|LSE|LSE|LSE|
|/ 2,4<br>rchs<br>|/ 2,4<br>rchs<br>|,8,16<br>HSI16|,8,16<br>HSI16|,8,16<br>HSI16|,8,16<br>HSI16|,8,16<br>HSI16|,8,16<br>HSI16|,8,16<br>HSI16|,8,16<br>HSI16|
|/ 1,4<br>4 MHz|/ 1,4<br>4 MHz|/ 1,4<br>4 MHz|/ 1,4<br>4 MHz|/ 1,4<br>4 MHz|/ 1,4<br>4 MHz|/ 1,4<br>4 MHz|/ 1,4<br>4 MHz|/ 1,4<br>4 MHz|/ 1,4<br>4 MHz|
|/ 1,4<br>4 MHz|/ 1,4<br>4 MHz|/ 1,4<br>4 MHz|/ 1,4<br>4 MHz|/ 1,4<br>4 MHz|/ 1,4<br>4 MHz|/ 1,4<br>4 MHz||||
|/ 1,4<br>4 MHz|/ 1,4<br>4 MHz|/ 1,4<br>4 MHz|HSE|HSE|HSE|HSE|HSE|||
|/ 1,4<br>4 MHz|/ 1,4<br>4 MHz|||||||||

1. For full details about the internal and external clock source characteristics, please refer to the “Electrical
characteristics” section in your device datasheet.

RM0377 Rev 10 171/905

215

--- end of page=170 ---

**Reset and clock control (RCC)** **RM0377**

The timer clock frequencies are automatically fixed by hardware. There are two cases:

1. If the APB prescaler is 1, the timer clock frequencies are set to the same frequency as
that of the APB domain to which the timers are connected.

2. Otherwise, they are set to twice (×2) the frequency of the APB domain to which the
timers are connected.

f CLK acts as Cortex [®] -M0+ free running clock. For more details refer to the _Section 27:_
_Debug support (DBG)_ .

**7.2.1** **HSE clock**

The high speed external clock signal (HSE) can be generated from two possible clock

sources:

      - HSE external crystal/ceramic resonator

      - HSE user external clock

The resonator and the load capacitors have to be placed as close as possible to the
oscillator pins in order to minimize output distortion and startup stabilization time. The
loading capacitance values must be adjusted according to the selected oscillator.

**Table 42. HSE/LSE clock sources**

|Clock source|Hardware configuration|
|---|---|
|External clock for<br>category 2 (LQFP48<br>only), category 3 and<br>5 devices|<br>MSv31915V1<br>OSC_IN<br>OSC_OUT<br>GPIO<br>External<br>source|

172/905 RM0377 Rev 10

--- end of page=171 ---

**RM0377** **Reset and clock control (RCC)**

**Table 42. HSE/LSE clock sources (continued)**

|Clock source|Hardware configuration|
|---|---|
|External clock for<br>category 1 and 2<br>devices (packages<br>with less that 48<br>pins)|<br>External<br>source<br>CK_IN<br>GPIO<br>MSv36151V1|
|Crystal/Ceramic<br>resonators for<br>category 2 (LQFP48<br>only), category 3 and<br>5 devices|<br>MSv31916V1<br>OSC_IN<br>OSC_OUT<br>CL1<br>CL2<br>Load<br>capacitors|

**External source (HSE bypass)**

In this mode, an external clock source must be provided. It can have a frequency of up to
32 MHz. This mode is selected by setting the HSEBYP and HSEON bits in the RCC_CR
register _(see Section 7.3.1: Clock control register (RCC_CR))_ . The external clock signal
with ~50% duty cycle has to drive the following pin (see _Figure 42_ ):

      - On devices where OSC_IN and OSC_OUT pins are available: the OSC_IN pin must be
driven while the OSC_OUT pin should be left hi-Z.

      - Otherwise, the CK_IN pin must be driven.

_Note:_ _For details on pin availability, refers to the pinout section in your device datasheet._

The external clock signal can be square, sinus or triangle. To minimize the consumption, it
is recommended to use the square signal.

**External crystal/ceramic resonator (HSE crystal)**

The 1 to 24 MHz external oscillator has the advantage of producing a very accurate rate on
the main clock.

The associated hardware configuration is shown in _Figure 42_ . Refer to the electrical
characteristics section of the _datasheet_ for more details.

The HSERDY flag of the RCC_CR register _(see Section 7.3.1)_ indicates whether the HSE
oscillator is stable or not. At startup, the HSE clock is not released until this bit is set by
hardware. An interrupt can be generated if enabled in the _RCC_CR register_ .

The HSE Crystal can be switched on and off using the HSEON bit in the _RCC_CR register_ .

For code example, refer to _A.4.1: HSE start sequence code example_ .

RM0377 Rev 10 173/905

215

--- end of page=172 ---

**Reset and clock control (RCC)** **RM0377**

**7.2.2** **HSI16 clock**

The HSI16 clock signal is generated from an internal 16 MHz RC oscillator. It can be used
directly as a system clock or as PLL input.

The HSI16 clock can be used after wake-up from the Stop low-power mode, this ensure a
smaller wake-up time than a wake-up using MSI clock.

The HSI16 RC oscillator has the advantage of providing a clock source at low cost (no
external components). It also has a faster startup time than the HSE crystal oscillator
however, even with calibration the frequency is less accurate than an external crystal
oscillator or ceramic resonator.

The HSI16 clock can be kept running in Stop mode by setting HSI16KERON bit in RCC_CR
register (see _Section 7.3.1: Clock control register (RCC_CR)_ ). In this case the HSI16 clock
can be used for dedicated peripherals which can run in Stop mode.

**Calibration**

RC oscillator frequencies can vary from one chip to another due to manufacturing process
variations, this is why each device is factory calibrated by ST for 1% accuracy at an ambient
temperature, T A, of 25 °C.

After reset, the factory calibration value is loaded in the HSI16CAL[7:0] bits in the Internal
Clock Sources Calibration Register (RCC_ICSCR) _(see Section 7.3.2)._

If the application is subject to voltage or temperature variations, this may affect the RC
oscillator speed. You can trim the HSI16 frequency in the application by using the
HSI16TRIM[4:0] bits in the RCC_ICSCR register. For more details on how to measure the
HSI16 frequency variation please refer to _Section 7.2.14: Internal/external clock_
_measurement using TIM21_ .

The HSI16RDY flag in the RCC_CR register indicates whether the HSI16 oscillator is stable
or not. At startup, the HSI16 RC output clock is not released until this bit is set by hardware.

The HSI16 RC oscillator can be switched on and off using the HSI16ON bit in the RCC_CR
register.

**7.2.3** **MSI clock**

The MSI clock signal is generated from an internal RC oscillator. Its frequency range can be
adjusted by software by using the MSIRANGE[2:0] bits in the RCC_ICSCR register (see
_Section 7.3.2: Internal clock sources calibration register (RCC_ICSCR)_ ). Seven frequency
ranges are available: 65.536 kHz, 131.072 kHz, 262.144 kHz, 524.288 kHz, 1.048 MHz,
2.097 MHz (default value) and 4.194 MHz.

The MSI clock is always used as system clock after restart from Reset and wake-up from
Standby. After wake-up from Stop mode, the MSI clock can be selected as system clock
instead of HSI16 (or HSI16/4).

When the device restarts after a reset or a wake-up from Standby, the MSI frequency is set
to its default value. The MSI frequency does not change after waking up from Stop.

The MSI RC oscillator has the advantage of providing a low-cost (no external components)
low-power clock source. It is used as wake-up clock in low-power modes to reduce power
consumption.

The MSIRDY flag in the RCC_CR register indicates whether the MSI RC is stable or not. At
startup, the MSI RC output clock is not released until this bit is set by hardware.

174/905 RM0377 Rev 10

--- end of page=173 ---

**RM0377** **Reset and clock control (RCC)**

The MSI RC can be switched on and off by using the MSION bit in the RCC_CR register
_(see Section 7.3.1_ ).

It can also be used as a backup clock source (auxiliary clock) if the HSE crystal oscillator
fails. Refer to _Section 7.2.9: HSE clock security system (CSS) on page 177_ .

**Calibration**

The MSI RC oscillator frequency can vary from one chip to another due to manufacturing
process variations, this is why each device is factory calibrated by ST for 1% accuracy at an
ambient temperature, T A, of 25 °C.

After reset, the factory calibration value is loaded in the MSICAL[7:0] bits in the
RCC_ICSCR register. If the application is subject to voltage or temperature variations, this
may affect the RC oscillator speed. You can trim the MSI frequency in the application by
using the MSITRIM[7:0] bits in the RCC_ICSCR register. For more details on how to
measure the MSI frequency variation please refer to _Section 7.2.14: Internal/external clock_
_measurement using TIM21_ .

**7.2.4** **PLL**

The internal PLL can be clocked by the HSI16 RC or HSE clocks.

The PLL input clock frequency must range between 2 and 24 MHz.

The desired frequency is obtained by using the multiplication factor and output division
embedded in the PLL:

      - The system clock is derived from the PLL VCO divided by the output division factor.

_Note:_ _The application software must set correctly the PLL multiplication factor to avoid exceeding_
_96 MHz as PLLVCO when the product is in range 1,_

_48 MHz as PLLVCO when the product is in range 2,_

_24 MHz when the product is in range 3._

_It must also set correctly the output division to avoid exceeding 32 MHz as SYSCLK._

_The minimum input clock frequency for PLL is 2 MHz (when using HSE as PLL source)._

The PLL configuration (selection of the source clock, multiplication factor and output division
factor) must be performed before enabling the PLL. Once the PLL is enabled, these
parameters cannot be changed.

To modify the PLL configuration, proceed as follows:

1. Disable the PLL by setting PLLON to 0.

2. Wait until PLLRDY is cleared. The PLL is now fully stopped.

3. Change the desired parameter.
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
