IvanLi-CN/ups120/docs/rm0377/RM0377_STM32L0x1_Part_005.md

# RM0377 STM32L0x1 — Pages 201–250

**RM0377** **Reset and clock control (RCC)**

**7.3.14** **APB1 peripheral clock enable register (RCC_APB1ENR)**

Address: 0x38

Reset value: 0x0000 0000

Access: word, half-word and byte access

No wait state, except if the access occurs while an access to a peripheral on APB1 domain
is on going. In this case, wait states are inserted until this access to APB1 peripheral is
finished.

_Note:_ _When the peripheral clock is not active, the peripheral register values may not be readable_
_by software and the returned value is always 0x0._

|31|30|29|28|27|26|25|24|23|22|21|20|19|18|17|16|
|---|---|---|---|---|---|---|---|---|---|---|---|---|---|---|---|
|LPTIM1<br>EN|I2C3E<br>N|Res.|PWRE<br>N|Res|Res.|Res.|Res.|Res.|I2C2E<br>N|I2C1E<br>N|USART5<br>EN|USART4<br>EN|LPUART1<br>EN|USART2<br>EN|Res.|
|rw|rw||rw||||||rw|rw|rw|rw|rw|rw||

|15|14|13|12|11|10|9|8|7|6|5|4|3|2|1|0|
|---|---|---|---|---|---|---|---|---|---|---|---|---|---|---|---|
|Res.|SPI2E<br>N|Res.|Res.|WWDG<br>EN|Res.|Res.|Res.|Res.|Res.|TIM7E<br>N|TIM6EN|Res.|Res.|TIM3EN|TIM2E<br>N|
||rw|||rw||||||rw|rw|||rw|rw|

Bit 31 **LPTIM1EN:** Low-power timer clock enable bit

This bit is set and cleared by software.
0: Low-power timer clock disabled
1: Low-power timer clock enabled

Bit 30 **I2C3EN:** I2C3 clock enable bit

This bit is set and cleared by software.

0: I2C3 clock disabled

1: I2C3 clock enabled

Bit 28 **PWREN:** Power interface clock enable bit

This bit is set and cleared by software.

0: Power interface clock disabled

1: Power interface clock enabled

Bit 27 Reserved, must be kept at reset value.

Bits 26:23 Reserved, must be kept at reset value.

Bit 22 **I2C2EN:** I2C2 clock enable bit

This bit is set and cleared by software.

0: I2C2 clock disabled

1: I2C2 clock enabled

Bit 21 **I2C1EN:** I2C1 clock enable bit

This bit is set and cleared by software.

0: I2C1 clock disabled

1: I2C1 clock enabled

Bit 20 **USART5EN:** USART5 clock enable bit

This bit is set and cleared by software.

0: USART5 clock disabled

1: USART5 clock enabled

RM0377 Rev 10 201/905

215

--- end of page=200 ---

**Reset and clock control (RCC)** **RM0377**

Bit 19 **USART4EN:** USART4 clock enable bit

This bit is set and cleared by software.

0: USART4 clock disabled

1: USART4 clock enabled

Bit 18 **LPUART1EN:** LPUART1 clock enable bit

This bit is set and cleared by software.

0: LPUART1 clock disabled

1: LPUART1 clock enabled

Bit 17 **USART2EN:** USART2 clock enable bit

This bit is set and cleared by software.

0: USART2 clock disabled

1: USART2 clock enabled

Bits 16:15 Reserved, must be kept at reset value.

Bit 14 **SPI2EN:** SPI2 clock enable bit

This bit is set and cleared by software.

0: SPI2 clock disabled

1: SPI2 clock enabled

Bits 13:12 Reserved, must be kept at reset value.

Bit 11 **WWDGEN:** Window watchdog clock enable bit

This bit is set and cleared by software.
0: Window watchdog clock disabled
1: Window watchdog clock enabled

Bits 10:9 Reserved, must be kept at reset value.

Bits 8:6 Reserved, must be kept at reset value.

Bit 5 **TIM7EN:** Timer 7 clock enable bit

Set and cleared by software.

0: Timer 7 clock disabled

1: Timer 7 clock enabled

Bit 4 **TIM6EN:** Timer 6 clock enable bit

Set and cleared by software.

0: Timer 6 clock disabled

1: Timer 6 clock enabled

Bits 3:2 Reserved, must be kept at reset value.

Bit 1 **TIM3EN:** Timer3 clock enable bit

Set and cleared by software.

0: Timer3 clock disabled

1: Timer3 clock enabled

Bit 0 **TIM2EN:** Timer2 clock enable bit

Set and cleared by software.

0: Timer2 clock disabled

1: Timer2 clock enabled

202/905 RM0377 Rev 10

--- end of page=201 ---

**RM0377** **Reset and clock control (RCC)**

**7.3.15** **GPIO clock enable in Sleep mode register (RCC_IOPSMENR)**

Address: 0x3C

Reset value: the bits corresponding to the available GPIO ports are set

Access: no wait state, word, half-word and byte access

|31|30|29|28|27|26|25|24|23|22|21|20|19|18|17|16|
|---|---|---|---|---|---|---|---|---|---|---|---|---|---|---|---|
|Res.|Res.|Res.|Res.|Res.|Res.|Res.|Res.|Res.|Res.|Res.|Res.|Res.|Res.|Res.|Res.|
|||||||||||||||||

|15|14|13|12|11|10|9|8|7|6|5|4|3|2|1|0|
|---|---|---|---|---|---|---|---|---|---|---|---|---|---|---|---|
|Res.|Res.|Res.|Res.|Res.|Res.|Res.|Res.|IOPHS<br>MEN|Res.|Res.|IOPES<br>MEN|IOPDS<br>MEN|IOPCS<br>MEN|IOPBS<br>MEN|IOPAS<br>MEN|
|||||||||rw|||rw|rw|rw|rw|rw|

Bits 31: 8 Reserved, must be kept at reset value.

Bit 7 **IOPHSMEN:** Port H clock enable during Sleep mode bit

This bit is set and cleared by software.
0: Port H clock is disabled in Sleep mode
1: Port H clock is enabled in Sleep mode (if enabled by IOPHEN)

Bits 6:5 Reserved, must be kept at reset value.

Bit 4 **IOPESMEN:** Port E clock enable during Sleep mode bit

This bit is set and cleared by software.
0: Port E clock is disabled in Sleep mode
1: Port E clock is enabled in Sleep mode (if enabled by IOPDEN)

Bit 3 **IOPDSMEN:** Port D clock enable during Sleep mode bit

This bit is set and cleared by software.
0: Port D clock is disabled in Sleep mode
1: Port D clock is enabled in Sleep mode (if enabled by IOPDEN)

Bit 2 **IOPCSMEN:** Port C clock enable during Sleep mode bit

This bit is set and cleared by software.
0: Port C clock is disabled in Sleep mode
1: Port C clock is enabled in Sleep mode (if enabled by IOPCEN)

Bit 1 **IOPBSMEN:** Port B clock enable during Sleep mode bit

This bit is set and cleared by software.
0: Port B clock is disabled in Sleep mode
1: Port B clock is enabled in Sleep mode (if enabled by IOPBEN)

Bit 0 **IOPASMEN:** Port A clock enable during Sleep mode bit

This bit is set and cleared by software.
0: Port A clock is disabled in Sleep mode
1: Port A clock is enabled in Sleep mode (if enabled by IOPAEN)

RM0377 Rev 10 203/905

215

--- end of page=202 ---

**Reset and clock control (RCC)** **RM0377**

**7.3.16** **AHB peripheral clock enable in Sleep mode**
**register (RCC_AHBSMENR)**

Address: 0x40

Reset value: the bits corresponding to the available peripherals are set

Access: no wait state, word, half-word and byte access

|31|30|29|28|27|26|25|24|23|22|21|20|19|18|17|16|
|---|---|---|---|---|---|---|---|---|---|---|---|---|---|---|---|
|Res.|Res.|Res.|Res.|Res.|Res.|Res.|CRYP<br>SMEN|Res.|Res.|Res.|Res.|Res.|Res.|Res.|Res.|
||||||||rw|||||||||

|15|14|13|12|11|10|9|8|7|6|5|4|3|2|1|0|
|---|---|---|---|---|---|---|---|---|---|---|---|---|---|---|---|
|Res.|Res.|Res.|CRC<br>SMEN|Res.|Res.|SRAM<br>SMEN|MIF<br>SMEN|Res.|Res.|Res.|Res.|Res.|Res.|Res.|DMA<br>SMEN|
||||rw|||rw|rw||||||||rw|

Bits 31:25 Reserved, must be kept at reset value.

Bit 24 **CRYPSMEN:** Crypto clock enable during Sleep mode bit

This bit is set and reset by software.
0: Crypto clock disabled in Sleep mode
1: Crypto clock enabled in Sleep mode

Bits 23:20 Reserved, must be kept at reset value.

Bits 19:16 Reserved, must be kept at reset value.

Bits 15: 13 Reserved, must be kept at reset value.

Bit 12 **CRCSMEN:** CRC clock enable during Sleep mode bit

This bit is set and reset by software.
0: Test integration module clock disabled in Sleep mode
1: Test integration module clock enabled in Sleep mode (if enabled by CRCEN)

Bits 11:10 Reserved, must be kept at reset value.

Bit 9 **SRAMSMEN:** SRAM interface clock enable during Sleep mode bit

This bit is set and reset by software.
0: NVM interface clock disabled in Sleep mode
1: NVM interface clock enabled in Sleep mode

Bit 8 **MIFSMEN:** NVM interface clock enable during Sleep mode bit

This bit is set and reset by software.
0: NVM interface clock disabled in Sleep mode
1: NVM interface clock enabled in Sleep mode

Bits 7:1 Reserved, must be kept at reset value.

Bit 0 **DMASMEN:** DMA clock enable during Sleep mode bit

This bit is set and reset by software.
0: DMA clock disabled in Sleep mode
1: DMA clock enabled in Sleep mode

204/905 RM0377 Rev 10

--- end of page=203 ---

**RM0377** **Reset and clock control (RCC)**

**7.3.17** **APB2 peripheral clock enable in Sleep mode**
**register (RCC_APB2SMENR)**

Address: 0x44

Reset value: the bits corresponding to the available peripherals are set.

Access: no wait state, word, half-word and byte access

|31|30|29|28|27|26|25|24|23|22|21|20|19|18|17|16|
|---|---|---|---|---|---|---|---|---|---|---|---|---|---|---|---|
|Res.|Res.|Res.|Res.|Res.|Res.|Res.|Res.|Res.|DBG<br>SMEN|Res.|Res.|Res.|Res.|Res.|Res.|
||||||||||rw|||||||

|15|14|13|12|11|10|9|8|7|6|5|4|3|2|1|0|
|---|---|---|---|---|---|---|---|---|---|---|---|---|---|---|---|
|Res.|USART1<br>SMEN|Res.|SPI1<br>SMEN|Res.|Res.|ADC<br>SMEN|Res.|Res.|Res.|TIM22<br>SMEN|Res.|Res.|TIM21<br>SMEN|Res.|SYSCF<br>SMEN|
||rw||rw|||rw||||rw|||rw||rw|

Bits 31:23 Reserved, must be kept at reset value.

Bit 22 **DBGSMEN:** DBG clock enable during Sleep mode bit

This bit is set and cleared by software.
0: DBG clock disabled in Sleep mode
1: DBG clock enabled in Sleep mode (if enabled by DBGEN)

Bits 21:15 Reserved, must be kept at reset value.

Bit 14 **USART1SMEN:** USART1 clock enable during Sleep mode bit

This bit is set and cleared by software.
0: USART1 clock disabled in Sleep mode
1: USART1 clock enabled in Sleep mode (if enabled by USART1EN)

Bit 13 Reserved, must be kept at reset value.

Bit 12 **SPI1SMEN:** SPI1 clock enable during Sleep mode bit

This bit is set and cleared by software.
0: SPI1 clock disabled in Sleep mode
1: SPI1 clock enabled in Sleep mode (if enabled by SPI1EN)

Bits 11:10 Reserved, must be kept at reset value.

Bit 9 **ADCSMEN:** ADC clock enable during Sleep mode bit

This bit is set and cleared by software.
0: ADC clock disabled in Sleep mode
1: ADC clock enabled in Sleep mode (if enabled by ADCEN)

Bits 8:6 Reserved, must be kept at reset value.

Bit 5 **TIM22SMEN:** TIM22 timer clock enable during Sleep mode bit

This bit is set and cleared by software.
0:TIM22 clock disabled in Sleep mode
1: TIM22 clock enabled in Sleep mode (if enabled by TIM22EN)

Bits 4:3 Reserved, must be kept at reset value.

RM0377 Rev 10 205/905

215

--- end of page=204 ---

**Reset and clock control (RCC)** **RM0377**

Bit 2 **TIM21SMEN:** TIM21 timer clock enable during Sleep mode bit

This bit is set and cleared by software.
0: TIM21 clock disabled in Sleep mode
1: TIM21 clock enabled in Sleep mode (if enabled by TIM21EN)

Bit 1 Reserved, must be kept at reset value.

Bit 0 **SYSCFGSMEN:** System configuration controller clock enable during Sleep mode bit

This bit is set and cleared by software.
0: System configuration controller clock disabled in Sleep mode
1: System configuration controller clock enabled in Sleep mode

**7.3.18** **APB1 peripheral clock enable in Sleep mode**
**register (RCC_APB1SMENR)**

Address: 0x48

Reset value: the bits corresponding to the available peripherals are set

_Note:_ Access: no wait state, word, half-word and byte access

|31|30|29|28|27|26|25|24|23|22|21|20|19|18|17|16|
|---|---|---|---|---|---|---|---|---|---|---|---|---|---|---|---|
|LPTIM1<br>SMEN|I2C3S<br>MEN|Res.|PWRS<br>MEN|Res.|Res.|Res.|Res.|Res.|I2C2S<br>MEN|I2C1S<br>MEN|USART5<br>SMEN|USART4<br>SMEN|LPUART1<br>SMEN|USART2<br>SMEN|Res.|
|rw|rw||rw||||||rw|rw|rw|rw|rw|rw||

|15|14|13|12|11|10|9|8|7|6|5|4|3|2|1|0|
|---|---|---|---|---|---|---|---|---|---|---|---|---|---|---|---|
|Res.|SPI2S<br>MEN|Res.|Res.|WWDG<br>SMEN|Res.|Res.|Res.|Res.||TIM7S<br>MEN|TIM6SM<br>EN|Res.|Res.|TIM3SM<br>EN|TIM2S<br>MEN|
||rw|||rw||||||rw|rw|||rw|rw|

Bit 31 **LPTIM1SMEN:** Low-power timer clock enable during Sleep mode bit

This bit is set and cleared by software.
0: Low-power timer clock disabled in Sleep mode
1: Low-power timer clock enabled in Sleep mode (if enabled by LPTIM1EN)

Bit 30 **I2C3SMEN:** I2C3 clock enable during Sleep mode bit

This bit is set and cleared by software.
0: I2C3 clock disabled in Sleep mode
1: I2C3 clock enabled in Sleep mode (if enabled by I2C3EN)

Bit 29 Reserved, must be kept at reset value.

Bit 28 **PWRSMEN:** Power interface clock enable during Sleep mode bit

This bit is set and cleared by software.
0: Power interface clock disabled in Sleep mode
1: Power interface clock enabled in Sleep mode (if enabled by PWREN)

Bit 27 Reserved, must be kept at reset value.

Bits 26:23 Reserved, must be kept at reset value.

Bit 22 **I2C2SMEN:** I2C2 clock enable during Sleep mode bit

This bit is set and cleared by software.
0: I2C2 clock disabled in Sleep mode
1: I2C2 clock enabled in Sleep mode (if enabled by I2C2EN)

206/905 RM0377 Rev 10

--- end of page=205 ---

**RM0377** **Reset and clock control (RCC)**

Bit 21 **I2C1SMEN:** I2C1 clock enable during Sleep mode bit

This bit is set and cleared by software.
0: I2C1 clock disabled in Sleep mode
1: I2C1 clock enabled in Sleep mode (if enabled by I2C1EN)

Bit 20 **USART5SMEN:** USART5 clock enable during Sleep mode bit

This bit is set and cleared by software.
0: USART5 clock disabled in Sleep mode
1: USART5 clock enabled in Sleep mode (if enabled by USART5EN)

Bit 19 **USART4SMEN:** USART4 clock enable during Sleep mode bit

This bit is set and cleared by software.
0: USART4 clock disabled in Sleep mode
1: USART4 clock enabled in Sleep mode (if enabled by USART4EN)

Bit 18 **LPUART1SMEN:** LPUART1 clock enable during Sleep mode bit

This bit is set and cleared by software.
0: LPUART1 clock disabled in Sleep mode
1: LPUART1 clock enabled in Sleep mode (if enabled by LPUART1EN)

Bit 17 **USART2SMEN:** USART2 clock enable during Sleep mode bit

This bit is set and cleared by software.
0: USART2 clock disabled in Sleep mode
1: USART2 clock enabled in Sleep mode (if enabled by USART2EN)

Bits 16:15 Reserved, must be kept at reset value.

Bit 14 **SPI2SMEN:** SPI2 clock enable during Sleep mode bit

This bit is set and cleared by software.
0: SPI2 clock disabled in Sleep mode
1: SPI2 clock enabled in Sleep mode (if enabled by SPI2SEN)

Bits 13:12 Reserved, must be kept at reset value.

Bit 11 **WWDGSMEN:** Window watchdog clock enable during Sleep mode bit

This bit is set and cleared by software.
0: Window watchdog clock disabled in Sleep mode
1: Window watchdog clock enabled in Sleep mode (if enabled by WWDGEN)

Bits 10:9 Reserved, must be kept at reset value.

Bits 8:6 Reserved, must be kept at reset value.

Bit 5 **TIM7SMEN:** Timer 7 clock enable during Sleep mode bit

Set and cleared by software.
0: Timer 7 clock disabled in Sleep mode
1: Timer 7 clock enabled in Sleep mode (if enabled by TIM7EN)

Bit 4 **TIM6SMEN:** Timer 6 clock enable during Sleep mode bit

Set and cleared by software.
0: Timer 6 clock disabled in Sleep mode
1: Timer 6 clock enabled in Sleep mode (if enabled by TIM6EN)

RM0377 Rev 10 207/905

215

--- end of page=206 ---

**Reset and clock control (RCC)** **RM0377**

Bits 3:2 Reserved, must be kept at reset value.

Bit 1 **TIM3SMEN:** Timer3 clock enable during Sleep mode bit

Set and cleared by software.
0: Timer3 clock disabled in Sleep mode
1: Timer3 clock enabled in Sleep mode (if enabled by TIM3EN)

Bit 0 **TIM2SMEN:** Timer2 clock enable during Sleep mode bit

Set and cleared by software.
0: Timer2 clock disabled in Sleep mode
1: Timer2 clock enabled in Sleep mode (if enabled by TIM2EN)

**7.3.19** **Clock configuration register (RCC_CCIPR)**

Address: 0x4C

Reset value: 0x0000 0000

Access: no wait state, word, half-word and byte access

|31|30|29|28|27|26|25|24|23|22|21|20|19|18|17|16|
|---|---|---|---|---|---|---|---|---|---|---|---|---|---|---|---|
|Res.|Res.|Res.|Res.|Res.|Res.|Res.|Res.|Res.|Res.|Res.|Res.|LPTIM1<br>SEL1|LPTIM1S<br>EL0|I2C3SE<br>L1|I2C3SE<br>L0|
|||||||||||||rw|rw|rw|rw|

|15|14|13|12|11|10|9|8|7|6|5|4|3|2|1|0|
|---|---|---|---|---|---|---|---|---|---|---|---|---|---|---|---|
|Res.|Res.|I2C1<br>SEL1|I2C1<br>SEL0|LPUART1<br>SEL1|LPUART1<br>SEL0|Res.|Res.|Res.|Res.|Res.|Res.|USART2<br>SEL1|USART2<br>SEL0|USART1<br>SEL1|USART1<br>SEL0|
|||rw|rw|rw|rw|||||||rw|rw|rw|rw|

Bits 31:26 Reserved, must be kept at reset value.

Bits 25:20 Reserved, must be kept at reset value.

Bits 19:18 **LPTIM1SEL:** Low-power Timer clock source selection bits

This bit is set and cleared by software.

00: APB clock selected as LP Timer clock

01: LSI clock selected as LP Timer clock

10: HSI16 clock selected as LP Timer clock

11: LSE clock selected as LP Timer clock
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
