IvanLi-CN/ups120/docs/assets/rm0377/rm0377-ultralowpower-stm32l0x1-advanced-armbased-32bit-mcus-stmicroelectronics.pdf-124-0.png

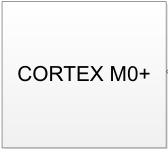
docs/assets/rm0377/rm0377-ultralowpower-stm32l0x1-advanced-armbased-32bit-mcus-stmicroelectronics.pdf-124-0.png
