IvanLi-CN/ups120/firmware/ups-main/docs/datasheets/images/5e60853963c6ec8153e1f730d277d1c3c8da14ee0a4a0e02d076ca6963cbb450.jpg

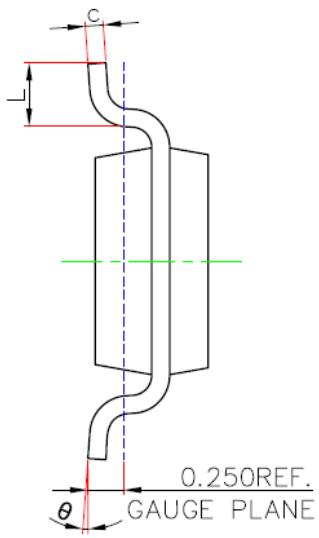
firmware/ups-main/docs/datasheets/images/5e60853963c6ec8153e1f730d277d1c3c8da14ee0a4a0e02d076ca6963cbb450.jpg
