IvanLi-CN/ups120/firmware/smart-battery/src/leds4_task.rs

//! 4-LED status task per SOFTWARE_DESIGN.md (3 s base cycle)
//!
//! LED map: 1→4 = Red, Yellow, Green, Blue.
//! Active-low GPIOs: low = ON, high = OFF.
//!
//! Priorities per LED: dropout 1 Hz > fault 50% > base + pulses.
//! Green additionally supports an async one-shot pulse on I2C1 activity.

use embassy_stm32::gpio::Output;
use embassy_time::{Duration, Instant, Timer};

const ENABLE_LED_DIAG: bool = false;

macro_rules! led_diag {
    ($($arg:tt)*) => {
        if ENABLE_LED_DIAG {
            defmt::info!($($arg)*);
        }
    };
}

use crate::shared::{
    BalancingCvRequestSubscriber, Bq76920AlertsSubscriber, Bq76920MeasurementsSubscriber,
    Sc8815AlertsSubscriber,
};
use crate::state_bits::{self, bits as sbits};
// Red LED base derives from ACTIVE_BQ (task activation), not MOS gating.

// Timing (3 s base cycle; pulses are 120 ms wide with 120 ms gaps)
const CYCLE_MS: u32 = 3000;
const FAULT_ON_MS: u32 = 1500; // 50% blink window
const PULSE_W_MS: u32 = 120;
const PULSE_GAP_MS: u32 = 120;

#[derive(Clone, Copy, Default)]
struct LedIntent {
    base_on: bool, // true → LED ON (low level)
    pulses: u8,    // 0..=8 pulses at cycle start
    fault_blink: bool,
    dropout_blink: bool, // reserved; to be driven by dropout counters
}

pub struct LedPins {
    pub red: Output<'static>,
    pub yellow: Output<'static>,
    pub green: Output<'static>,
    pub blue: Output<'static>,
}

fn apply_led(pin: &mut Output<'static>, on: bool) {
    if on {
        pin.set_low();
    } else {
        pin.set_high();
    }
}

fn compose_with_pulses(base_on: bool, pulses: u8, phase_ms: u32) -> bool {
    if pulses == 0 {
        return base_on;
    }
    let window_ms = PULSE_W_MS + PULSE_GAP_MS;
    let slot = (phase_ms / window_ms) as u8;
    if slot < pulses {
        // inside pulse band
        let in_pulse = (phase_ms % window_ms) < PULSE_W_MS;
        return if in_pulse { !base_on } else { base_on };
    }
    base_on
}

// Note: FET gating状态仅通过 red.base_on 表达；不再需要单独判定“both_on”作为脉冲编码输入。

/// 4-LED status compositor
#[embassy_executor::task]
pub async fn leds_task(
    mut pins: LedPins,
    mut bq_sub: Bq76920MeasurementsSubscriber<'static, 5>,
    mut sc_alerts_sub: Sc8815AlertsSubscriber<'static>,
    mut bq_alerts_sub: Bq76920AlertsSubscriber<'static>,
    mut bal_cv_sub: BalancingCvRequestSubscriber<'static>,
) {
    // Per-LED 3 s epochs
    let epoch_red = Instant::now();
    let epoch_yellow = epoch_red;
    let epoch_green = epoch_red;
    let epoch_blue = epoch_red;

    // Async green pulse state
    let mut green_pulse_until: Option<Instant> = None;

    // Latest sources
    let mut bq: Option<crate::data_types::Bq76920Measurements<5>> = None;
    // sc_dropout computed per-loop from heartbeat
    // SC/BQ derived flags
    let mut sc_ac_present = false;
    let mut sc_fault = false; // OTP or VBUS short
    let mut sc_expected = false;
    let mut sc_confirmed = false;
    let mut sc_pause_ov = false;
    let mut sc_pause_imb = false;
    let mut sc_pause_temp = false;
    let mut sc_overtemp_adin = false;
    let mut bq_fault = false;
    let mut overlay_balancing = false;
    let mut temp_pause_active = false; // from BQ (BalancingCvRequest)

    // Edge log for BQ dropout (drives Red LED 1 Hz blink)
    let mut prev_bq_dropout = false;

    // Duty sampler for Red LED: estimate actual on-duty per ~1s window
    let mut red_on_ticks: u16 = 0;
    let mut red_samples: u16 = 0;
    let mut red_last_report = Instant::now();

    loop {
        let now = Instant::now();
        // Non-blocking drains
        if let Some(m) = bq_sub.try_next_message_pure() {
            bq = Some(m);
        }
        // Cache decoded flags for this iteration to avoid jitter and repeated reads
        let mut sc_vbus_short = false;
        let mut sc_otp = false;
        if let Some(a) = sc_alerts_sub.try_next_message_pure() {
            sc_ac_present = a.device_status.ac_adapter_connected;
            sc_vbus_short = a.device_status.vbus_short_fault;
            sc_otp = a.device_status.otp_fault;
            sc_fault = sc_vbus_short || sc_otp;
            sc_expected = a.expected_charging;
            sc_confirmed = a.charging_confirmed;
            sc_pause_ov = a.ov_pause_active;
            sc_pause_imb = a.imbalance_pause_active;
            sc_pause_temp = a.temp_pause_adin;
            sc_overtemp_adin = a.overtemp_adin;
        }
        let mut red_pulse_severity: u8 = 0; // 4>3>2>1
        if let Some(ba) = bq_alerts_sub.try_next_message_pure() {
            use bq769x0_async_rs::registers::SysStatFlags;
            let f = ba.system_status.0;
            if f.contains(SysStatFlags::SCD) {
                red_pulse_severity = red_pulse_severity.max(3);
            }
            if f.contains(SysStatFlags::OCD) {
                red_pulse_severity = red_pulse_severity.max(4);
            }
            if f.intersects(SysStatFlags::UV | SysStatFlags::OV) {
                red_pulse_severity = red_pulse_severity.max(2);
            }
            bq_fault = f.intersects(
                SysStatFlags::UV | SysStatFlags::OV | SysStatFlags::SCD | SysStatFlags::OCD,
            );
        }
        if let Some(b) = bal_cv_sub.try_next_message_pure() {
            overlay_balancing = b.overlay;
            temp_pause_active = b.temp_pause;
        }
        // Dropout derived from online flags: device stays online after boot probe
        // and only turns offline on real communication timeout thereafter.
        let bq_dropout = !crate::failsafe::is_bq_online();
        if bq_dropout && !prev_bq_dropout {
            defmt::warn!("led:red dropout on");
        } else if !bq_dropout && prev_bq_dropout {
            led_diag!("led:red dropout off");
        }
        prev_bq_dropout = bq_dropout;
        let sc_dropout = !crate::failsafe::is_sc_online();

        // Trigger async green pulse on I2C1 activity
        if crate::activity::I2C1_ACTIVITY_PULSE.load(core::sync::atomic::Ordering::Relaxed) {
            crate::activity::I2C1_ACTIVITY_PULSE
                .store(false, core::sync::atomic::Ordering::Relaxed);
            green_pulse_until = Some(Instant::now() + Duration::from_millis(PULSE_W_MS as u64));
        }

        let p_red = (now - epoch_red).as_millis() as u32 % CYCLE_MS;
        let p_yellow = (now - epoch_yellow).as_millis() as u32 % CYCLE_MS;
        let p_green = (now - epoch_green).as_millis() as u32 % CYCLE_MS;
        let p_blue = (now - epoch_blue).as_millis() as u32 % CYCLE_MS;

        let state_flags = state_bits::flags();

        // Red (BQ activation/protection)
        let mut red = LedIntent::default();
        // Base ON semantics: ACTIVE_BQ → ON; otherwise OFF.
        // ACTIVE_BQ reflects task activation (e.g., 1s cadence for balancing/charging phase),
        // it is independent from MOS/FET gating.
        let red_active = (state_flags & sbits::ACTIVE_BQ) != 0;
        red.base_on = red_active;
        // Fault blink mapping：电池故障 → 50% 闪烁；并按严重度分配脉冲数（越严重脉冲数越大）
        if bq_fault {
            red.fault_blink = true;
        }
        if bq_dropout {
            red.dropout_blink = true;
        }
        // Pulse code（severity）：3=SCD，4=OCD，2=UV/OV，其次 1=均衡叠加
        if red_pulse_severity > 0 {
            red.pulses = red.pulses.max(red_pulse_severity);
        }
        if overlay_balancing {
            red.pulses = red.pulses.max(1);
        }
        // Report temperature pause via Red LED with a dedicated code (6 pulses).
        if temp_pause_active {
            red.pulses = red.pulses.max(6);
        }
        // Note: do NOT assign extra pulses when FETs are not both ON.
        //       Base_on already reflects FET gating (any side OFF → base ON),
        //       to avoid mixing with temperature indication.

        // Yellow (SC8815)
        let yellow_active = (state_flags & sbits::ACTIVE_SC) != 0;
        let mut yellow = LedIntent {
            base_on: yellow_active,
            ..Default::default()
        };
        if sc_fault {
            yellow.fault_blink = true;
        }
        if sc_dropout {
            yellow.dropout_blink = true;
        }
        // Yellow pulses：
        // - 2 = 适配器异常（VBUS short）
        // - 4 = 过温
        // - 1 = preparing（需要充电但 AC 不在）
        if !sc_ac_present
            && bq
                .as_ref()
                .is_some_and(|m| m.core_measurements.total_voltage_mv < 17_000)
        {
            yellow.pulses = yellow.pulses.max(1);
        }
        if sc_vbus_short {
            yellow.pulses = yellow.pulses.max(2);
        }
        if sc_otp || sc_pause_temp || sc_overtemp_adin {
            yellow.pulses = yellow.pulses.max(4);
        }

        // Green (Comm + Sleep)
        let green = LedIntent {
            base_on: !crate::sleep_manager::is_sleeping(),
            ..Default::default()
        };
        // async pulse handled after composition

        // Blue (Global)
        let mut blue = LedIntent {
            base_on: false,
            ..Default::default()
        };
        let fault_bits = sbits::FAULT_BQ | sbits::FAULT_SC;
        let blue_code: u8 = if (state_flags & fault_bits) != 0 || bq_fault || sc_fault {
            6
        } else if (state_flags & sbits::BALANCING) != 0 || overlay_balancing {
            4
        } else if sc_pause_ov
            || sc_pause_imb
            || sc_pause_temp
            || (state_flags & sbits::CHG_PAUSED) != 0
        {
            3
        } else if (state_flags & sbits::FULL) != 0 {
            5
        } else if (state_flags & sbits::CHARGING) != 0
            || (sc_ac_present && (sc_expected || sc_confirmed))
        {
            2
        } else {
            1
        };
        blue.pulses = blue_code;
        state_bits::set_blue_code(blue_code);

        // Drive pins with priority
        // RED
        let red_on = if red.dropout_blink {
            // 1 Hz blink (reserve; not set yet)
            ((p_red / 500) & 1) == 0
        } else if red.fault_blink {
            p_red < FAULT_ON_MS
        } else {
            compose_with_pulses(red.base_on, red.pulses, p_red)
        };
        apply_led(&mut pins.red, red_on);

        // Red duty sampling & 1s report (helps distinguish 50% vs ~30% pulses)
        red_samples = red_samples.saturating_add(1);
        if red_on {
            red_on_ticks = red_on_ticks.saturating_add(1);
        }
        if (now - red_last_report) >= Duration::from_millis(1000) {
            let duty_pct: u32 = if red_samples > 0 {
                (u32::from(red_on_ticks) * 100) / u32::from(red_samples)
            } else {
                0
            };
            led_diag!(
                "led:red duty={}%% d/o/p={}{}{} base={} pulses={} p={}",
                duty_pct,
                if red.dropout_blink { 'D' } else { '-' },
                if red.fault_blink { 'F' } else { '-' },
                if red.pulses > 0 { 'P' } else { '-' },
                red.base_on,
                red.pulses,
                p_red
            );
            red_on_ticks = 0;
            red_samples = 0;
            red_last_report = now;
        }

        // YELLOW
        let yellow_on = if yellow.dropout_blink {
            ((p_yellow / 500) & 1) == 0
        } else if yellow.fault_blink {
            p_yellow < FAULT_ON_MS
        } else {
            compose_with_pulses(yellow.base_on, yellow.pulses, p_yellow)
        };
        apply_led(&mut pins.yellow, yellow_on);

        // GREEN (with async pulse overlay)
        let mut green_on = compose_with_pulses(green.base_on, green.pulses, p_green);
        if let Some(until) = green_pulse_until {
            if now < until {
                green_on = !green_on;
            } else {
                green_pulse_until = None;
            }
        }
        apply_led(&mut pins.green, green_on);

        // BLUE
        let blue_on = if blue.dropout_blink {
            ((p_blue / 500) & 1) == 0
        } else if blue.fault_blink {
            p_blue < FAULT_ON_MS
        } else {
            compose_with_pulses(blue.base_on, blue.pulses, p_blue)
        };
        apply_led(&mut pins.blue, blue_on);

        // Tick
        Timer::after(Duration::from_millis(10)).await;
    }
}
