IvanLi-CN/ups120/firmware/smart-battery/src/sleep_manager.rs

use defmt::*;
use embassy_sync::blocking_mutex::raw::CriticalSectionRawMutex;
use embassy_sync::signal::Signal;
use embassy_time::{Duration, Instant, Timer};
use portable_atomic::{AtomicBool, AtomicU32};

static ACTIVE_COUNT: AtomicU32 = AtomicU32::new(0);
static SLEEPING: AtomicBool = AtomicBool::new(false);
static mut LAST_ACTIVITY_MS: u32 = 0;
static mut FORBID_SLEEP_UNTIL_MS: u32 = 0; // wake-holdoff deadline (ms)
static WAKE_LATCH: AtomicBool = AtomicBool::new(false); // set by holders at work start
static WAKE_CAUSE_PRINTED: AtomicBool = AtomicBool::new(false); // throttle cause log per sleep cycle

const SLEEP_REENTER_IDLE_MS: u32 = 300;
const WAKE_HOLDOFF_MS: u32 = 8000; // Keep awake >=8s after activity

static NOTIFY: Signal<CriticalSectionRawMutex, ()> = Signal::new();

pub struct BusyGuard;

impl BusyGuard {
    fn new() -> Self {
        BusyGuard
    }
}

impl Drop for BusyGuard {
    fn drop(&mut self) {
        ACTIVE_COUNT.fetch_sub(1, portable_atomic::Ordering::Relaxed);
        NOTIFY.signal(());
        bump("drop");
    }
}

pub fn hold(_who: &str) -> BusyGuard {
    ACTIVE_COUNT.fetch_add(1, portable_atomic::Ordering::Relaxed);
    unsafe {
        LAST_ACTIVITY_MS = Instant::now().as_millis() as u32;
    }
    unsafe {
        FORBID_SLEEP_UNTIL_MS = LAST_ACTIVITY_MS.saturating_add(WAKE_HOLDOFF_MS);
    }
    let was = WAKE_LATCH.swap(true, portable_atomic::Ordering::Relaxed);
    if !was && !WAKE_CAUSE_PRINTED.swap(true, portable_atomic::Ordering::Relaxed) {
        debug!("wake: cause={}()", _who);
    }
    NOTIFY.signal(());
    BusyGuard::new()
}

pub fn bump(_who: &str) {
    unsafe {
        LAST_ACTIVITY_MS = Instant::now().as_millis() as u32;
    }
    NOTIFY.signal(());
}
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
